ductuanhoang/29.Esp32_Webpage/Code/components/user_driver/LSM6DSLSensor.h

/**
 ******************************************************************************
 * @file    LSM6DSLSensor.h
 * @author  AST
 * @version V1.0.0
 * @date    7 September 2017
 * @brief   Abstract Class of an LSM6DSL Inertial Measurement Unit (IMU) 6 axes
 *          sensor.
 ******************************************************************************
 * @attention
 *
 * <h2><center>&copy; COPYRIGHT(c) 2017 STMicroelectronics</center></h2>
 *
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
 ******************************************************************************
 */

/* Prevent recursive inclusion -----------------------------------------------*/

#ifndef __LSM6DSLSensor_H__
#define __LSM6DSLSensor_H__
#ifdef __cplusplus
extern "C"
{
#endif
    /* Includes ------------------------------------------------------------------*/

#include "LSM6DSL_ACC_GYRO_Driver.h"

    /* Defines -------------------------------------------------------------------*/

#define LSM6DSL_ACC_SENSITIVITY_FOR_FS_2G 0.061  /**< Sensitivity value for 2 g full scale [mg/LSB] */
#define LSM6DSL_ACC_SENSITIVITY_FOR_FS_4G 0.122  /**< Sensitivity value for 4 g full scale [mg/LSB] */
#define LSM6DSL_ACC_SENSITIVITY_FOR_FS_8G 0.244  /**< Sensitivity value for 8 g full scale [mg/LSB] */
#define LSM6DSL_ACC_SENSITIVITY_FOR_FS_16G 0.488 /**< Sensitivity value for 16 g full scale [mg/LSB] */

#define LSM6DSL_GYRO_SENSITIVITY_FOR_FS_125DPS 04.375  /**< Sensitivity value for 125 dps full scale [mdps/LSB] */
#define LSM6DSL_GYRO_SENSITIVITY_FOR_FS_245DPS 08.750  /**< Sensitivity value for 245 dps full scale [mdps/LSB] */
#define LSM6DSL_GYRO_SENSITIVITY_FOR_FS_500DPS 17.500  /**< Sensitivity value for 500 dps full scale [mdps/LSB] */
#define LSM6DSL_GYRO_SENSITIVITY_FOR_FS_1000DPS 35.000 /**< Sensitivity value for 1000 dps full scale [mdps/LSB] */
#define LSM6DSL_GYRO_SENSITIVITY_FOR_FS_2000DPS 70.000 /**< Sensitivity value for 2000 dps full scale [mdps/LSB] */

#define LSM6DSL_PEDOMETER_THRESHOLD_LOW 0x00 /**< Lowest  value of pedometer threshold */
#define LSM6DSL_PEDOMETER_THRESHOLD_MID_LOW 0x07
#define LSM6DSL_PEDOMETER_THRESHOLD_MID 0x0F
#define LSM6DSL_PEDOMETER_THRESHOLD_MID_HIGH 0x17
#define LSM6DSL_PEDOMETER_THRESHOLD_HIGH 0x1F /**< Highest value of pedometer threshold */

#define LSM6DSL_WAKE_UP_THRESHOLD_LOW 0x01 /**< Lowest  value of wake up threshold */
#define LSM6DSL_WAKE_UP_THRESHOLD_MID_LOW 0x0F
#define LSM6DSL_WAKE_UP_THRESHOLD_MID 0x1F
#define LSM6DSL_WAKE_UP_THRESHOLD_MID_HIGH 0x2F
#define LSM6DSL_WAKE_UP_THRESHOLD_HIGH 0x3F /**< Highest value of wake up threshold */

#define LSM6DSL_TAP_THRESHOLD_LOW 0x01 /**< Lowest  value of wake up threshold */
#define LSM6DSL_TAP_THRESHOLD_MID_LOW 0x08
#define LSM6DSL_TAP_THRESHOLD_MID 0x10
#define LSM6DSL_TAP_THRESHOLD_MID_HIGH 0x18
#define LSM6DSL_TAP_THRESHOLD_HIGH 0x1F /**< Highest value of wake up threshold */

#define LSM6DSL_TAP_SHOCK_TIME_LOW 0x00 /**< Lowest  value of wake up threshold */
#define LSM6DSL_TAP_SHOCK_TIME_MID_LOW 0x01
#define LSM6DSL_TAP_SHOCK_TIME_MID_HIGH 0x02
#define LSM6DSL_TAP_SHOCK_TIME_HIGH 0x03 /**< Highest value of wake up threshold */

#define LSM6DSL_TAP_QUIET_TIME_LOW 0x00 /**< Lowest  value of wake up threshold */
#define LSM6DSL_TAP_QUIET_TIME_MID_LOW 0x01
#define LSM6DSL_TAP_QUIET_TIME_MID_HIGH 0x02
#define LSM6DSL_TAP_QUIET_TIME_HIGH 0x03 /**< Highest value of wake up threshold */

#define LSM6DSL_TAP_DURATION_TIME_LOW 0x00 /**< Lowest  value of wake up threshold */
#define LSM6DSL_TAP_DURATION_TIME_MID_LOW 0x04
#define LSM6DSL_TAP_DURATION_TIME_MID 0x08
#define LSM6DSL_TAP_DURATION_TIME_MID_HIGH 0x0C
#define LSM6DSL_TAP_DURATION_TIME_HIGH 0x0F /**< Highest value of wake up threshold */

    /* Typedefs ------------------------------------------------------------------*/
    typedef enum
    {
        LSM6DSL_STATUS_OK = 0,
        LSM6DSL_STATUS_ERROR,
        LSM6DSL_STATUS_TIMEOUT,
        LSM6DSL_STATUS_NOT_IMPLEMENTED
    } LSM6DSLStatusTypeDef;

    typedef enum
    {
        LSM6DSL_INT1_PIN,
        LSM6DSL_INT2_PIN
    } LSM6DSL_Interrupt_Pin_t;

    typedef struct
    {
        unsigned int FreeFallStatus : 1;
        unsigned int TapStatus : 1;
        unsigned int DoubleTapStatus : 1;
        unsigned int WakeUpStatus : 1;
        unsigned int StepStatus : 1;
        unsigned int TiltStatus : 1;
        unsigned int D6DOrientationStatus : 1;
    } LSM6DSL_Event_Status_t;

    /* Class Declaration ---------------------------------------------------------*/

    /**
 * Abstract class of an LSM6DSL Inertial Measurement Unit (IMU) 6 axes
 * sensor.
 */
    LSM6DSLStatusTypeDef LSM6DSLSensor_begin(void);
    LSM6DSLStatusTypeDef LSM6DSLSensor_end(void);
    LSM6DSLStatusTypeDef LSM6DSLSensor_Enable_X(void);
    LSM6DSLStatusTypeDef LSM6DSLSensor_Enable_G(void);
    LSM6DSLStatusTypeDef LSM6DSLSensor_Disable_X(void);
    LSM6DSLStatusTypeDef LSM6DSLSensor_Disable_G(void);
    LSM6DSLStatusTypeDef LSM6DSLSensor_ReadID(uint8_t *p_id);
    LSM6DSLStatusTypeDef LSM6DSLSensor_Get_X_Axes(int32_t *pData);
    LSM6DSLStatusTypeDef LSM6DSLSensor_Get_G_Axes(int32_t *pData);
    LSM6DSLStatusTypeDef LSM6DSLSensor_Get_X_Sensitivity(float *pfData);
    LSM6DSLStatusTypeDef LSM6DSLSensor_Get_G_Sensitivity(float *pfData);
    LSM6DSLStatusTypeDef LSM6DSLSensor_Get_X_AxesRaw(int16_t *pData);
    LSM6DSLStatusTypeDef LSM6DSLSensor_Get_G_AxesRaw(int16_t *pData);
    LSM6DSLStatusTypeDef LSM6DSLSensor_Get_X_ODR(float *odr);
    LSM6DSLStatusTypeDef LSM6DSLSensor_Get_G_ODR(float *odr);
    LSM6DSLStatusTypeDef LSM6DSLSensor_Set_X_ODR(float odr);
    LSM6DSLStatusTypeDef LSM6DSLSensor_Set_G_ODR(float odr);
    LSM6DSLStatusTypeDef LSM6DSLSensor_Get_X_FS(float *fullScale);
    LSM6DSLStatusTypeDef LSM6DSLSensor_Get_G_FS(float *fullScale);
    LSM6DSLStatusTypeDef LSM6DSLSensor_Set_X_FS(float fullScale);
    LSM6DSLStatusTypeDef LSM6DSLSensor_Set_G_FS(float fullScale);
    LSM6DSLStatusTypeDef LSM6DSLSensor_Enable_Free_Fall_Detection_Int1_Pin(void);
    LSM6DSLStatusTypeDef LSM6DSLSensor_Enable_Free_Fall_Detection(LSM6DSL_Interrupt_Pin_t int_pin);
    LSM6DSLStatusTypeDef LSM6DSLSensor_Disable_Free_Fall_Detection(void);
    LSM6DSLStatusTypeDef LSM6DSLSensor_Set_Free_Fall_Threshold(uint8_t thr);
    LSM6DSLStatusTypeDef LSM6DSLSensor_Enable_Pedometer(void);
    LSM6DSLStatusTypeDef LSM6DSLSensor_Disable_Pedometer(void);
    LSM6DSLStatusTypeDef LSM6DSLSensor_Get_Step_Counter(uint16_t *step_count);
    LSM6DSLStatusTypeDef LSM6DSLSensor_Reset_Step_Counter(void);
    LSM6DSLStatusTypeDef LSM6DSLSensor_Set_Pedometer_Threshold(uint8_t thr);
    LSM6DSLStatusTypeDef LSM6DSLSensor_Enable_Tilt_Detection_Int1_Pin(void);
    LSM6DSLStatusTypeDef LSM6DSLSensor_Enable_Tilt_Detection(LSM6DSL_Interrupt_Pin_t int_pin);
    LSM6DSLStatusTypeDef LSM6DSLSensor_Disable_Tilt_Detection(void);
    LSM6DSLStatusTypeDef LSM6DSLSensor_Enable_Wake_Up_Detection_Int2_PIN(void);
    LSM6DSLStatusTypeDef LSM6DSLSensor_Enable_Wake_Up_Detection(LSM6DSL_Interrupt_Pin_t int_pin);
    LSM6DSLStatusTypeDef LSM6DSLSensor_Disable_Wake_Up_Detection(void);
    LSM6DSLStatusTypeDef LSM6DSLSensor_Set_Wake_Up_Threshold(uint8_t thr);
    LSM6DSLStatusTypeDef LSM6DSLSensor_Enable_Single_Tap_Detection_Int1_PIN(void);
    LSM6DSLStatusTypeDef LSM6DSLSensor_Enable_Single_Tap_Detection(LSM6DSL_Interrupt_Pin_t int_pin);
    LSM6DSLStatusTypeDef LSM6DSLSensor_Disable_Single_Tap_Detection(void);
    LSM6DSLStatusTypeDef LSM6DSLSensor_Enable_Double_Tap_Detection_Int1_Pin(void);
    LSM6DSLStatusTypeDef LSM6DSLSensor_Enable_Double_Tap_Detection(LSM6DSL_Interrupt_Pin_t int_pin);
    LSM6DSLStatusTypeDef LSM6DSLSensor_Disable_Double_Tap_Detection(void);
    LSM6DSLStatusTypeDef LSM6DSLSensor_Set_Tap_Threshold(uint8_t thr);
    LSM6DSLStatusTypeDef LSM6DSLSensor_Set_Tap_Shock_Time(uint8_t time);
    LSM6DSLStatusTypeDef LSM6DSLSensor_Set_Tap_Quiet_Time(uint8_t time);
    LSM6DSLStatusTypeDef LSM6DSLSensor_Set_Tap_Duration_Time(uint8_t time);
    LSM6DSLStatusTypeDef LSM6DSLSensor_Enable_6D_Orientation_Int1_PIN(void);
    LSM6DSLStatusTypeDef LSM6DSLSensor_Enable_6D_Orientation(LSM6DSL_Interrupt_Pin_t int_pin);
    LSM6DSLStatusTypeDef LSM6DSLSensor_Disable_6D_Orientation(void);
    LSM6DSLStatusTypeDef LSM6DSLSensor_Get_6D_Orientation_XL(uint8_t *xl);
    LSM6DSLStatusTypeDef LSM6DSLSensor_Get_6D_Orientation_XH(uint8_t *xh);
    LSM6DSLStatusTypeDef LSM6DSLSensor_Get_6D_Orientation_YL(uint8_t *yl);
    LSM6DSLStatusTypeDef LSM6DSLSensor_Get_6D_Orientation_YH(uint8_t *yh);
    LSM6DSLStatusTypeDef LSM6DSLSensor_Get_6D_Orientation_ZL(uint8_t *zl);
    LSM6DSLStatusTypeDef LSM6DSLSensor_Get_6D_Orientation_ZH(uint8_t *zh);
    LSM6DSLStatusTypeDef LSM6DSLSensor_Get_Event_Status(LSM6DSL_Event_Status_t *status);
    LSM6DSLStatusTypeDef LSM6DSLSensor_ReadReg(uint8_t reg, uint8_t *data);
    LSM6DSLStatusTypeDef LSM6DSLSensor_WriteReg(uint8_t reg, uint8_t data);
    LSM6DSLStatusTypeDef LSM6DSLSensor_GetTemp(uint16_t *temp);

#ifdef __cplusplus
}
#endif

#endif
