ductuanhoang/29.Esp32_Webpage/Code/components/peripheral/user_pwm.c

/*
 * led_driver.c
 *
 *  Created on: Jan 9, 2021
 *      Author: ductu
 */
/***********************************************************************************************************************
* Pragma directive
***********************************************************************************************************************/

/***********************************************************************************************************************
* Includes <System Includes>
***********************************************************************************************************************/
#include "user_pwm.h"
#include "driver/ledc.h"
#include "esp_err.h"
#include <math.h>       /* pow */
/***********************************************************************************************************************
* Macro definitions
***********************************************************************************************************************/

/***********************************************************************************************************************
* Typedef definitions
***********************************************************************************************************************/
#define LEDC_TIMER              LEDC_TIMER_0
#define LEDC_MODE               LEDC_LOW_SPEED_MODE
#define LEDC_OUTPUT_IO          (25) // Define the output GPIO
#define LEDC_CHANNEL            LEDC_CHANNEL_0
#define LEDC_DUTY_RES           LEDC_TIMER_13_BIT // Set duty resolution to 13 bits
#define LEDC_DUTY               (4095) // Set duty to 50%. ((2 ** 13) - 1) * 50% = 4095
#define LEDC_FREQUENCY          (5000) // Frequency in Hertz. Set frequency at 5 kHz
/***********************************************************************************************************************
* Private global variables and functions
***********************************************************************************************************************/


/***********************************************************************************************************************
* Exported global variables and functions (to be accessed by other files)
***********************************************************************************************************************/

/***********************************************************************************************************************
* Imported global variables and functions (from other files)
***********************************************************************************************************************/

/***********************************************************************************************************************
* Function Name: 
* Description  :
* Arguments    : none
* Return Value : none
***********************************************************************************************************************/
void user_pwm_init(void)
{
    // Prepare and then apply the LEDC PWM timer configuration
    ledc_timer_config_t ledc_timer = {
        .speed_mode       = LEDC_MODE,
        .timer_num        = LEDC_TIMER,
        .duty_resolution  = LEDC_DUTY_RES,
        .freq_hz          = LEDC_FREQUENCY,  // Set output frequency at 5 kHz
        .clk_cfg          = LEDC_AUTO_CLK
    };
    ESP_ERROR_CHECK(ledc_timer_config(&ledc_timer));

    // Prepare and then apply the LEDC PWM channel configuration
    ledc_channel_config_t ledc_channel = {
        .speed_mode     = LEDC_MODE,
        .channel        = LEDC_CHANNEL,
        .timer_sel      = LEDC_TIMER,
        .intr_type      = LEDC_INTR_DISABLE,
        .gpio_num       = LEDC_OUTPUT_IO,
        .duty           = 0, // Set duty to 0%
        .hpoint         = 0
    };
    ESP_ERROR_CHECK(ledc_channel_config(&ledc_channel));
}

void user_pwm_start(void)
{
    ledc_fade_start(LEDC_MODE, LEDC_CHANNEL, LEDC_FADE_WAIT_DONE);
    // Set duty to 50%
    ESP_ERROR_CHECK(ledc_set_duty(LEDC_MODE, LEDC_CHANNEL, 0));
    // Update duty to apply the new value
    ESP_ERROR_CHECK(ledc_update_duty(LEDC_MODE, 0));
}

void user_pwm_stop(void)
{
    ledc_stop(LEDC_MODE, LEDC_CHANNEL, 0);
}

void user_pwm_set_duty(uint8_t _duty)
{
    uint32_t duty_tranform = 0;
    duty_tranform = ((pow(2, 13) - 1) * _duty) / 100;
    APP_LOGI("duty_tranform = %d", duty_tranform);
    // Set duty to 50%
    ESP_ERROR_CHECK(ledc_set_duty(LEDC_MODE, LEDC_CHANNEL, duty_tranform));
    // Update duty to apply the new value
    ESP_ERROR_CHECK(ledc_update_duty(LEDC_MODE, LEDC_CHANNEL));
}
/***********************************************************************************************************************
* Static Functions
***********************************************************************************************************************/
/***********************************************************************************************************************
* Function Name:
* Description  :
* Arguments    : none
* Return Value : none
***********************************************************************************************************************/

/***********************************************************************************************************************
* End of file
***********************************************************************************************************************/
