ductuanhoang/29.Esp32_Webpage/Code/components/user_driver/user_leds.c

/*
 * led_driver.c
 *
 *  Created on: Jan 9, 2021
 *      Author: ductu
 */
/***********************************************************************************************************************
* Pragma directive
***********************************************************************************************************************/

/***********************************************************************************************************************
* Includes <System Includes>
***********************************************************************************************************************/
#include "user_leds.h"
/***********************************************************************************************************************
* Macro definitions
***********************************************************************************************************************/

/***********************************************************************************************************************
* Typedef definitions
***********************************************************************************************************************/

/***********************************************************************************************************************
* Private global variables and functions
***********************************************************************************************************************/

/***********************************************************************************************************************
* Exported global variables and functions (to be accessed by other files)
***********************************************************************************************************************/

/***********************************************************************************************************************
* Imported global variables and functions (from other files)
***********************************************************************************************************************/

/***********************************************************************************************************************
* Function Name: 
* Description  :
* Arguments    : none
* Return Value : none
***********************************************************************************************************************/
void leds_gpio_init(void)
{    
    //zero-initialize the config structure.
    gpio_config_t io_conf = {};
    //disable interrupt
    io_conf.intr_type = GPIO_INTR_DISABLE;
    //set as output mode
    io_conf.mode = GPIO_MODE_OUTPUT;
    //bit mask of the pins that you want to set,e.g.GPIO18/19
    io_conf.pin_bit_mask = GPIO_OUTPUT_PIN_SEL;
    //disable pull-down mode
    io_conf.pull_down_en = 0;
    //disable pull-up mode
    io_conf.pull_up_en = 0;
    esp_err_t error = gpio_config(&io_conf); //configure GPIO with the given settings
    if (error != ESP_OK)
    {
        APP_LOGE("error configuring outputs\n");
    }
}


void led_red(bool _status)
{
    gpio_set_level(GPIO_USER_LED_RED, _status);
}

void led_green(bool _status)
{
    gpio_set_level(GPIO_USER_LED_GREEN, _status);
}

void led_blue(bool _status)
{
    gpio_set_level(GPIO_USER_LED_BLUE, _status);
}
/***********************************************************************************************************************
* Static Functions
***********************************************************************************************************************/
/***********************************************************************************************************************
* Function Name:
* Description  :
* Arguments    : none
* Return Value : none
***********************************************************************************************************************/

/***********************************************************************************************************************
* End of file
***********************************************************************************************************************/
