ductuanhoang/29.Esp32_Webpage/Code/components/task/mqtt_task.h

/*
 * mqtt_task.h
 *
 *  Created on: Nov 24, 2020
 *      Author: Yolo
 */

#ifndef MAIN_TASK_MQTT_TASK_H_
#define MAIN_TASK_MQTT_TASK_H_
/****************************************************************************/
/***        Include files                                                 ***/
/****************************************************************************/
#include "../../Common.h"

/****************************************************************************/
/***        Macro Definitions                                             ***/
/****************************************************************************/

/****************************************************************************/
/***        Type Definitions                                              ***/
/****************************************************************************/

/****************************************************************************/
/***         Exported global functions                                     ***/
/****************************************************************************/
void mqtt_task_start(void);

void mqtt_send_message(char *event_id);
#endif /* MAIN_TASK_MQTT_TASK_H_ */
